marcelvanherk/nova1200-restoration/teensy_nova/Photo_Teensy40.jpg

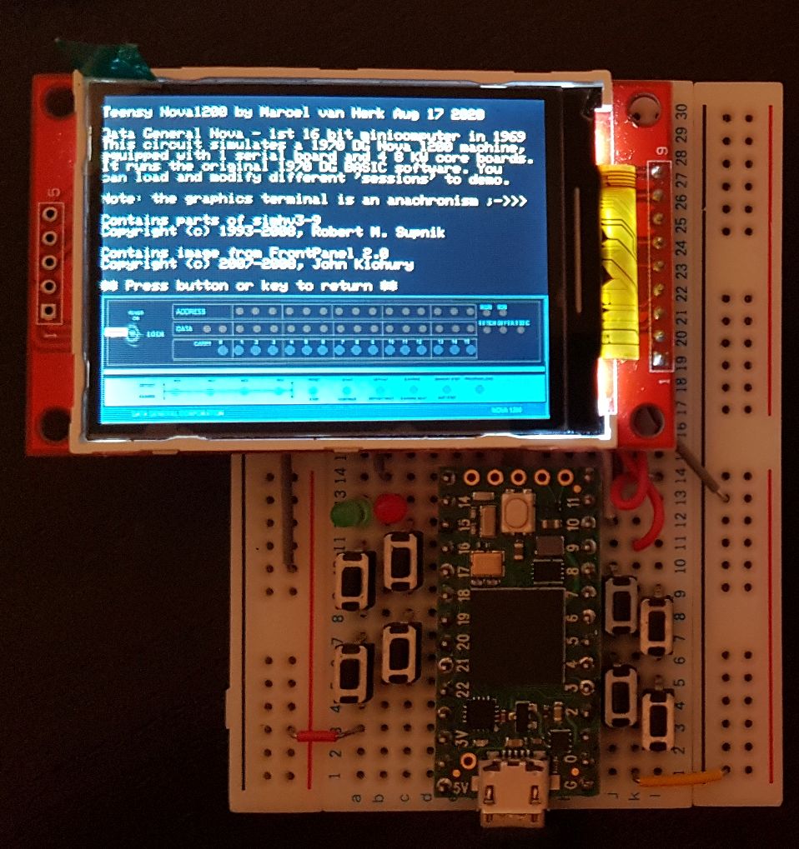
teensy_nova/Photo_Teensy40.jpg
