marcelvanherk/nova1200-restoration/teensy_nova/Pico_nova_bb.png

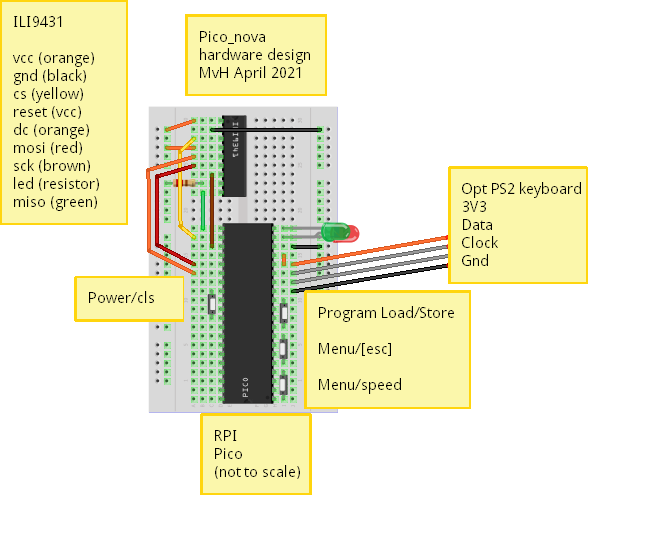
teensy_nova/Pico_nova_bb.png
