marcelvanherk/nova1200-restoration/teensy_nova/teensy_nova_bb.png

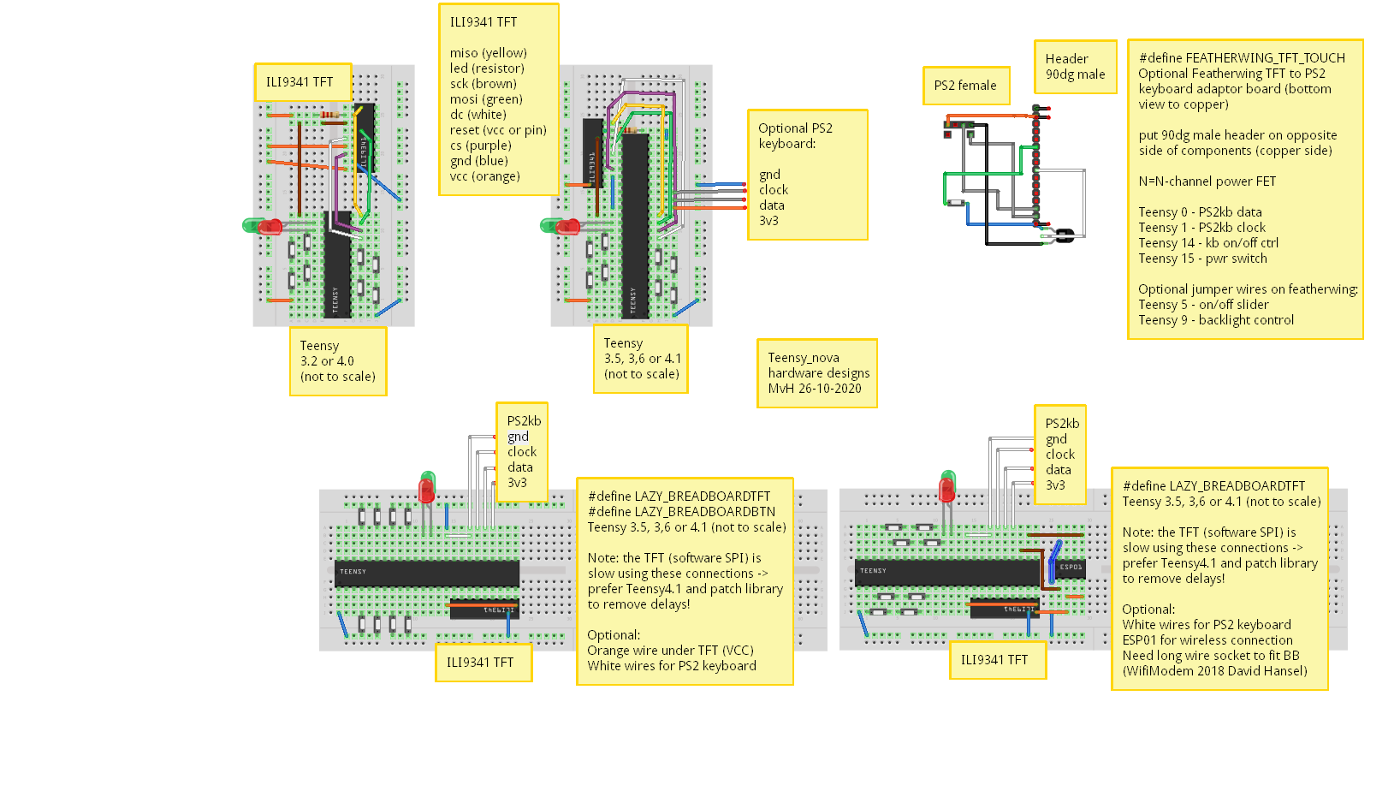
teensy_nova/teensy_nova_bb.png
