marcelvanherk/nova1200-restoration/arduino_nova1200rev3pcb/Minimal_components.png

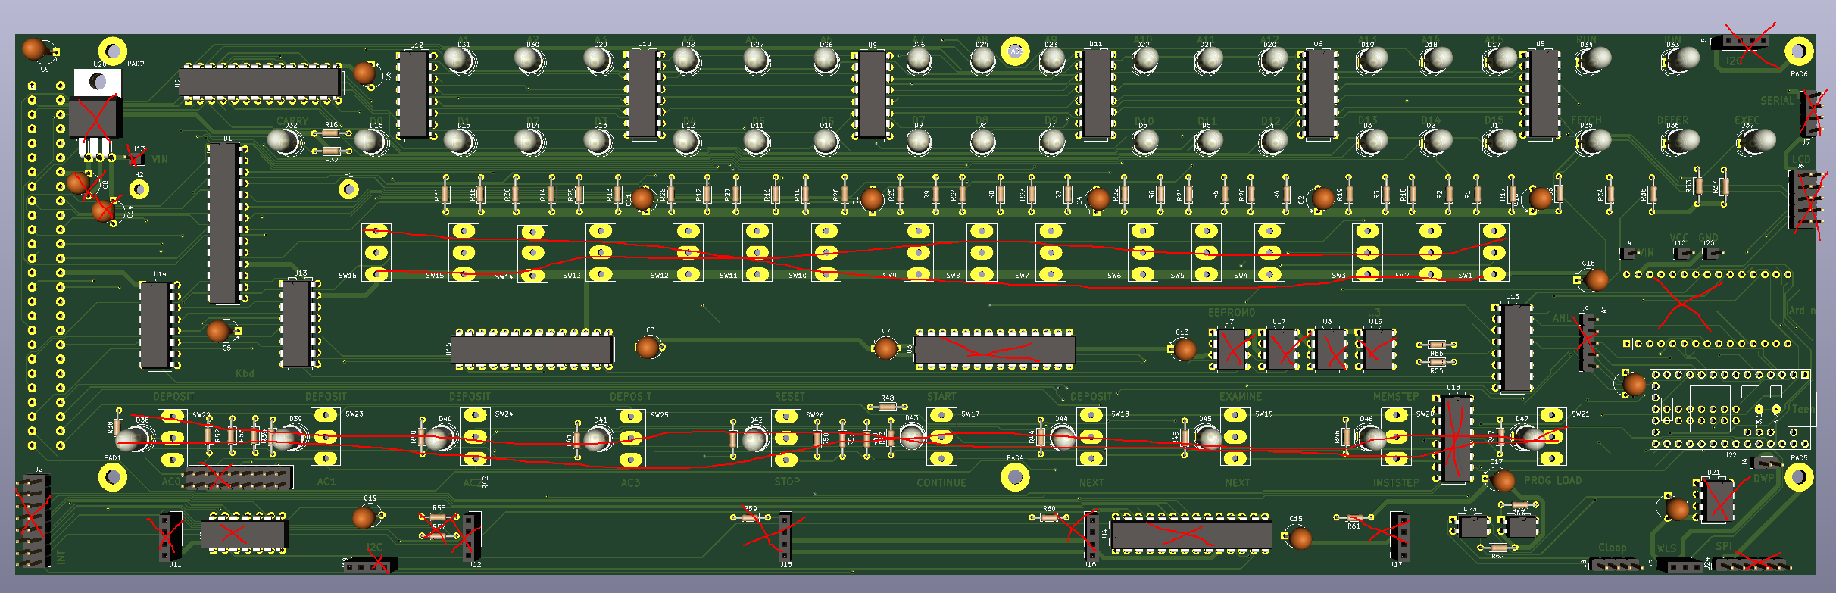
arduino_nova1200rev3pcb/Minimal_components.png
