marcelvanherk/nova1200-restoration/teensy_nova/recondemo.h

// demo version of nova reconstructor NovaReconstructDemo.lua
// Marcel van Herk 21 Jab 2025
// start with go 02000
// configurable variables start at address 02001
// 2501222 added sinogram display
// 2501225 sinogram displays right-hand; redisplay at 2015; load at 2017

const PROGMEM unsigned short recondemo[] = {

//>unload
53224,0,
32768,64,0,
64,13,1248,1528,1423,0,0,2048,7356,0,1806,15360,416,0,0,
77,2,596,90,
32847,4,0,
83,12,1388,128,1610,8970,272,1796,1578,9118,1593,4,1814,8576,
95,12,1028,1541,1567,1,2047,80,0,0,1993,1030,2,6400,
107,12,1033,100,0,1034,65280,1026,180,1050,255,0,59136,0,
119,12,1031,1518,0,1835,1032,70,0,0,1025,61440,61952,62464,
131,12,62976,63488,64000,64512,336,1000,0,98,0,170,65408,10,
143,9,66,0,248,64,0,65520,0,65436,1035,
32920,4,0,
156,2,1780,1615,
32926,17,0,
175,2,16,1854,
32945,210,0,
387,12,65394,65255,65118,64985,64853,64725,64599,64476,64355,64238,64123,64012,
399,1,63903,
33168,16,0,
416,12,32,65426,65287,65150,65017,64885,64757,64631,64508,64387,64270,64155,
428,12,64044,63935,63830,63727,63627,63531,63437,63347,63260,63176,63096,63018,
440,12,62944,62873,62806,62742,62681,62624,62570,62519,62472,62428,62388,62351,
452,12,62317,62288,62261,62238,62219,62203,62191,62182,62177,62175,62177,62182,
464,12,62191,62203,62219,62238,62261,62288,62317,62351,62388,62428,62472,62519,
476,12,62570,62624,62681,62742,62806,62873,62944,63018,63096,63176,63260,63347,
488,12,63437,63531,63627,63727,63830,63935,64044,64155,64270,64387,64508,64631,
500,12,64757,64885,65017,65150,65287,65426,32,176,323,472,623,777,
512,12,933,1091,1252,1414,1579,1746,1914,2085,2257,2431,2607,2785,
524,12,2964,3145,3328,3512,3697,3884,4072,4262,4452,4644,4837,5031,
536,12,5226,5421,5618,5815,6013,6212,6412,6612,6812,7013,7214,7416,
548,12,7618,7820,8022,8224,8426,8628,8830,9032,9234,9435,9636,9836,
560,12,10036,10236,10435,10633,10830,11027,11222,11417,11611,11804,11996,12186,
572,12,12376,12564,12751,12936,13120,13303,13484,13663,13841,14017,14191,14363,
584,12,14534,14702,14869,15034,15196,15357,15515,15671,15825,15976,16125,16272,
596,12,0,458,915,1372,1829,2285,2740,3195,3648,4101,4552,5002,
608,12,5450,5897,6342,6785,7226,7664,8101,8535,8966,9394,9820,10243,
620,12,10662,11079,11492,11901,12307,12709,13107,13501,13892,14277,14659,15036,
632,12,15408,15776,16139,16497,16850,17198,17541,17878,18210,18536,18857,19172,
644,12,19481,19784,20081,20372,20657,20936,21208,21474,21733,21985,22231,22470,
656,12,22702,22928,23146,23357,23561,23758,23948,24130,24306,24473,24633,24786,
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
//Length (words): 1828
};
