marcelvanherk/nova1200-restoration/teensy_nova/nova_sinogram3.h

// CT 180 projections 1.17 mm detector pitch

const PROGMEM unsigned short nova_sinogram3[]={

1,1,1,1,1,1,1,1,1,1,1,2,2,3,7,26,24,100,410,252,76,65,61,60,58,57,58,60,57,57,54,50,49,77,173,256,333,478,651,658,669,705,735,757,787,812,838,843,863,865,868,883,881,889,911,913,909,905,899,873,850,854,865,870,876,896,897,881,899,912,881,875,886,885,873,877,876,878,881,872,879,890,881,871,869,867,869,869,843,798,793,798,820,824,790,739,700,697,598,425,329,210,69,50,50,51,52,53,54,57,60,70,195,429,167,9,5,4,3,3,2,2,2,2,2,1,2,1,
1,1,1,1,1,1,1,1,1,1,1,2,2,3,15,28,18,167,418,206,68,62,62,61,58,57,59,60,57,57,53,50,52,91,185,265,347,506,654,653,664,706,734,752,777,804,834,840,845,867,868,882,887,884,903,914,911,907,905,889,863,857,867,874,876,882,901,896,887,904,891,872,874,887,875,873,874,870,880,876,874,882,889,883,880,873,867,863,847,809,790,801,817,831,796,738,712,698,568,404,318,199,69,49,50,51,52,52,55,57,62,80,246,381,117,6,4,4,3,3,2,2,2,2,2,2,1,1,
1,1,1,1,1,1,1,1,1,1,1,2,2,6,22,23,27,242,395,177,62,59,62,61,59,58,59,61,58,56,52,50,55,105,196,274,361,535,659,648,662,706,732,745,767,795,823,829,827,860,872,880,889,884,895,913,911,910,908,902,881,865,869,877,876,876,898,908,884,886,898,875,869,881,883,869,869,868,874,883,875,877,894,895,887,876,864,857,848,823,794,799,813,836,802,740,724,702,540,384,308,186,67,49,50,51,52,53,56,58,65,101,283,324,87,2,2,3,3,2,2,2,2,2,2,1,1,1,
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

};
