marcelvanherk/nova1200-restoration/teensy_nova/nova_sinogram4.h

// CT 180 projections 1.17 mm detector pitch

const PROGMEM unsigned short nova_sinogram4[]={

1,1,1,1,1,1,1,1,1,4,12,11,5,3,3,4,7,121,420,236,73,63,60,59,57,57,58,58,56,56,53,49,50,89,213,348,396,439,549,631,639,684,732,775,804,835,829,840,887,901,916,943,939,925,916,906,901,894,887,880,874,783,683,667,687,713,726,790,805,749,740,743,703,692,802,829,832,865,893,902,900,902,908,915,920,887,846,830,841,827,779,726,753,769,753,736,654,537,453,405,341,220,83,50,50,50,50,52,52,54,61,73,227,425,138,7,4,4,3,3,2,2,2,2,2,1,1,1,
1,1,1,1,1,1,1,1,4,12,12,5,2,3,3,4,12,191,417,194,65,61,60,59,58,57,58,59,56,56,52,49,55,106,214,340,400,455,573,630,648,692,734,779,801,821,828,847,889,905,920,945,943,931,919,909,905,897,893,884,875,804,693,659,665,705,734,776,806,761,743,743,731,697,770,826,830,861,889,897,899,905,911,915,911,882,839,819,839,829,786,747,765,759,752,724,628,516,445,400,339,214,88,50,50,50,50,51,52,56,63,87,275,369,96,5,3,3,3,2,2,2,2,2,2,2,1,1,
1,1,1,1,1,1,1,4,12,11,5,2,2,3,3,3,30,264,387,167,61,58,61,60,58,57,58,59,57,55,52,49,61,124,213,332,404,472,597,629,657,699,737,782,794,807,818,848,886,907,925,947,947,936,921,911,909,901,898,888,874,824,707,659,648,691,737,768,799,769,743,744,749,715,742,824,830,856,885,896,903,908,911,910,900,876,833,813,833,829,790,775,773,749,752,709,605,496,436,396,336,208,91,50,49,49,50,51,53,58,66,112,304,308,69,1,2,3,3,2,2,2,2,2,2,1,1,1,
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

};
