marcelvanherk/nova1200-restoration/teensy_nova/nova_sinogram2.h

// CT 180 projections 2.06 mm detector pitch

const PROGMEM unsigned short nova_sinogram2[]={

2,2,2,1,2,2,2,2,2,2,2,2,2,3,3,3,3,3,2,5,9,13,19,20,70,103,115,265,359,358,441,638,764,792,786,816,875,881,874,885,906,933,950,959,966,971,975,979,989,1002,1013,1021,1026,1030,1036,1039,1041,1048,1057,1065,1071,1076,1080,1086,1101,1107,1102,1092,1081,1074,1069,1062,1055,1049,1045,1044,1040,1037,1034,1028,1021,1012,1002,989,982,977,972,968,967,959,940,931,916,887,874,895,892,874,880,781,533,369,319,268,210,77,10,19,25,20,14,10,6,4,4,4,4,3,3,3,3,3,3,2,2,2,2,2,
1,2,2,2,1,2,2,2,2,2,2,3,3,3,3,3,3,3,3,2,5,8,11,18,48,108,113,203,346,415,450,608,760,807,803,839,888,876,869,885,906,926,946,958,964,970,975,981,993,1005,1014,1022,1025,1032,1036,1038,1043,1050,1057,1064,1069,1073,1078,1094,1105,1110,1103,1088,1081,1076,1068,1061,1057,1052,1047,1045,1040,1038,1034,1028,1022,1012,999,991,984,978,973,971,968,958,950,935,911,883,880,892,871,849,871,795,562,379,282,222,208,146,33,9,22,28,23,15,11,6,4,4,4,3,3,3,3,3,3,2,2,2,2,2,
0,1,2,2,2,2,2,2,2,3,3,3,3,3,3,3,3,3,3,2,2,4,7,8,23,93,124,188,292,402,485,610,756,822,820,866,902,868,864,885,905,921,937,953,963,969,975,985,997,1006,1015,1020,1027,1033,1035,1038,1046,1052,1056,1061,1066,1071,1084,1096,1105,1110,1100,1089,1081,1075,1068,1062,1057,1054,1050,1045,1042,1038,1033,1028,1022,1010,999,993,987,979,974,973,967,958,952,939,905,882,882,888,853,827,858,811,594,392,287,180,149,172,104,16,9,21,28,24,15,11,6,4,4,3,3,3,3,3,3,2,2,2,2,2,
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
};
