marcelvanherk/nova1200-restoration/teensy_nova/sos_xbasic.tape.h

// SOS Extended BASIC Interpreter from 1976; courtesy Bruce Ray

// values betweem {} created in lua as follows:
//local f = io.open([[E:\software\nova1200-restoration\SOS_XBASIC.AB]], 'rb')
//local t = f:read('*a')
//f:close()
//b={}
//for i=1, #t do
//  b[i]=t:byte(i)
//end
//print(#t, table.concat(b,','))

const PROGMEM unsigned char sos_xbasictape[]={0,0,0,0,0,0,0,0,0,0,0,0,0,0,0,0,0,0,0,0,0,0,0,0,0,0,0,0,0,0,0,0,0,0,0,0,0,0,0,0,0,0,0,0,0,0,0,0,0,0,0,0,0,0,0,0,0,0,
0,0,0,0,0,0,0,0,0,0,0,0,0,0,0,0,0,0,0,0,0,0,0,0,0,0,0,0,0,0,0,0,0,0,0,0,0,0,0,0,0,0,0,0,0,0,0,0,0,0,0,0,0,0,0,0,0,0,0,0,0,0,0,0,0,0,0,0,0,0,240,255,0,0,221,143,0,
0,222,7,12,9,37,8,47,8,0,0,240,4,0,0,207,8,180,8,0,1,54,2,182,254,52,50,0,0,98,4,0,0,0,0,240,255,16,0,44,255,0,0,0,0,2,0,3,0,4,0,5,0,6,0,7,0,0,0,10,0,13,0,16,0,32,
0,34,0,36,0,44,0,0,0,0,0,240,255,32,0,149,148,46,0,48,0,64,0,127,0,128,0,226,0,231,0,233,0,68,10,69,10,79,10,78,10,123,10,157,10,109,20,97,20,0,0,0,0,240,255,48,0,
71,179,99,20,101,20,103,20,107,20,145,20,105,20,66,20,0,21,249,20,9,21,12,21,64,21,241,20,234,20,84,21,70,21,0,0,0,0,240,255,64,0,46,10,110,21,112,21,118,21,0,0,0
,0,0,0,0,0,155,21,41,22,43,22,44,22,47,23,85,23,94,23,81,23,0,0,0,0,0,0,240,255,80,0,9,129,191,23,175,23,0,0,3,24,95,24,141,26,129,27,132,27,135,27,102,28,207,29,
215,29,232,29,238,29,236,29,0,0,0,0,0,0,240,255,96,0,227,177,0,0,0,0,0,0,0,0,0,0,177,32,181,32,169,32,173,32,116,31,0,0,229,31,125,34,106,35,183,34,26,35,0,0,0,0,
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
,7,206,5,139,7,0,0,0,0,0,0,0,0,0,0,0,0,0,0,0,0,0,0,0,0,0,0,0,0,0,0,0,0,240,255,160,3,112,252,0,0,0,0,0,0,0,0,0,0,0,0,0,0,0,0,0,0,0,0,0,0,0,0,0,0,0,0,0,0,0,0,0,0,0,0,240
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
