marcelvanherk/nova1200-restoration/teensy_nova/novabasic2.tape.h

// single user basic 2 from 1971

const PROGMEM unsigned char basic2tape[]={0,0,0,0,0,0,0,0,0,0,0,0,0,0,0,0,
248,255,0,0,25,40,2,0,99,1,3,4,58,15,231,64,
218,64,230,64,166,0,240,255,16,0,28,254,0,0,3,0,
4,0,5,0,6,0,7,0,10,0,11,0,15,0,18,0,
20,0,64,0,65,0,81,0,85,0,90,0,240,255,32,0,
248,245,94,0,124,0,127,0,128,0,135,0,138,0,141,0,
152,0,155,0,160,0,164,0,176,0,197,0,218,0,220,0,
223,0,240,255,48,0,228,117,224,0,226,0,228,0,231,0,
233,0,234,0,235,0,237,0,239,0,242,0,244,0,246,0,
252,0,254,0,255,0,0,124,253,255,64,0,183,114,0,255,
138,141,130,0,240,255,72,0,131,112,217,2,56,9,24,13,
25,13,119,12,135,12,152,12,97,11,182,3,189,4,43,1,
62,1,57,12,13,12,114,11,120,9,240,255,88,0,53,144,
176,11,177,10,158,11,132,11,105,1,22,7,29,9,149,11,
143,5,99,2,88,11,222,1,146,7,61,2,174,3,42,2,
246,255,104,0,130,218,223,7,161,2,134,0,32,2,150,1,
65,11,150,2,111,3,157,3,129,1,240,255,138,0,2,34,
0,0,0,0,0,0,0,0,224,48,224,16,147,0,228,48,
228,16,144,210,0,42,3,170,192,170,62,48,0,183,216,32,
241,255,154,0,191,161,41,40,5,130,12,181,0,3,255,3,
45,32,245,40,26,197,26,205,0,3,0,181,1,3,127,96,
167,0,0,0,240,255,170,0,109,178,251,0,249,0,241,0,
248,0,232,0,250,0,52,11,56,11,44,11,48,11,185,10,
120,2,202,10,119,2,0,0,0,0,240,255,186,0,84,129,
0,0,0,0,0,0,0,0,0,0,0,0,58,15,87,15,
88,15,126,15,152,15,158,15,160,15,171,15,253,0,29,1,
243,255,202,0,251,171,60,1,58,15,58,15,86,15,87,15,
112,1,109,2,41,2,44,2,183,12,2,0,0,0,0,0,
240,255,232,0,143,187,174,0,162,0,188,190,190,0,190,189,
189,0,188,189,188,0,187,0,172,0,168,0,219,0,172,0,
192,0,169,0,221,0,249,255,248,0,128,251,173,0,171,0,
175,0,170,0,222,0,0,0,0,0,240,255,63,1,122,237,
6,33,43,40,26,197,26,204,0,3,1,3,185,0,67,79,
80,89,82,73,71,72,84,32,40,67,41,32,49,57,54,57,
240,255,79,1,43,91,44,49,57,55,48,44,49,57,55,49,
44,49,57,55,50,44,49,57,55,51,65,76,76,32,82,73,
71,72,84,83,32,82,240,255,95,1,186,225,69,83,69,82,
86,69,68,0,67,64,68,72,69,80,70,88,112,133,71,64,
255,103,16,1,200,103,82,1,201,103,24,1,240,255,111,1,
128,210,63,99,4,130,63,102,71,32,128,130,67,32,68,40,
69,48,70,56,127,96,0,4,0,32,5,65,3,33,0,64,
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
