marcelvanherk/nova1200-restoration/teensy_nova/basic.session.h

const PROGMEM unsigned short basicsession[] = {
4938,0,
0,8,451,326,26047,34048,16615,16602,16614,166,
32776,9,0,
17,12,3,4,5,6,7,10,11,15,18,20,64,65,
29,12,81,85,90,94,124,127,128,135,138,141,152,155,
41,12,160,164,176,197,218,220,223,224,226,228,231,233,
53,12,234,235,237,239,242,244,246,252,254,255,31744,65280,
65,12,36234,130,0,65533,141,451,0,700,2331,3323,3324,3162,
77,12,3178,3195,2884,921,1184,299,318,3100,3056,2901,2395,2963,
89,12,2708,2945,2919,332,1785,2304,2936,1394,582,2875,449,1909,
101,12,544,913,525,1986,644,134,515,377,2852,633,850,896,
113,1,356,
32882,6,0,
120,2,3909,1,
32890,20,0,
142,12,12512,4320,147,12516,4324,53904,10752,43523,43712,12350,46848,8408,
154,12,10281,33285,46348,768,1023,8237,10485,50458,52506,768,46336,769,
166,12,24703,167,0,0,251,249,241,248,232,250,2839,2843,
178,6,2831,2835,2716,603,2733,602,
32952,8,0,
192,13,3869,32495,32496,32534,32560,32584,32592,32639,253,285,316,3869,3869,
205,12,32493,32495,368,592,524,527,3255,2,14,70,0,130,
217,2,0,1,
32987,4,0,
223,12,32495,634,32495,32592,32584,64992,133,0,0,174,162,48828,
235,12,190,48574,189,48572,188,187,172,168,219,172,192,169,
247,12,221,173,171,175,170,222,3338,3338,20310,17746,22354,18772,
259,12,17696,21576,17696,18005,20035,21577,20302,21280,21321,20012,17231,21292,
271,12,16724,20000,16718,17440,21569,20000,10324,22864,17696,22816,20306,8270,
283,12,10559,8192,3338,17487,8281,20309,8279,18771,18464,17231,19789,16679,
295,12,21280,21583,8258,17696,12596,8275,20545,17221,21280,10324,22864,17696,
307,12,22825,11296,20306,8241,13600,10324,22864,17696,20009,16128,0,0,
319,12,8454,10283,50458,52250,768,769,185,16451,18500,20549,22598,34160,
331,12,16455,26623,272,26568,338,26569,280,25407,33284,26175,8263,33408,
343,12,8259,10308,12357,14406,24703,1024,8192,16645,8451,16384,26175,1137,
355,12,0,8703,16384,34048,16615,493,24713,8423,33285,1116,12517,4325,
367,12,2195,20711,53765,259,2323,1116,10458,52229,24648,1116,26441,511,
379,12,16613,22759,16600,37376,2195,4325,24767,2308,14567,24703,768,22805,
391,12,8412,10454,35866,265,20753,12326,2320,12325,2318,12556,34048,16604,
403,12,10281,52251,4316,10277,52485,18652,2308,1281,372,0,26441,511,
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
