marcelvanherk/nova1200-restoration/teensy_nova/nova.image.h

/* GIMP RGB C-Source image dump (nova1200_fp.c) */

static const struct {
  unsigned int 	 width;
  unsigned int 	 height;
  unsigned int 	 bytes_per_pixel; /* 2:RGB16, 3:RGB, 4:RGBA */ 
  unsigned char	 pixel_data[320 * 93 * 2 + 1];
} gimp_image = {
  320, 93, 2,
  "\064\245\222\224\222\234\221\234\221\234\221\234\222\224\222\224\222\224\222"
  "\224\222\224\222\224\222\224\222\224\222\224\222\224\222\224\222\224\222"
  "\224\222\224\222\224\222\224\222\224\222\224\222\224\222\224\222\224\222"
  "\224\222\224\222\224\222\224\222\224\222\224\222\224\222\224\222\224\222"
  "\224\222\224\222\224\222\224\222\224\222\224\222\224\222\224\222\224\222"
  "\224\222\224\222\224\222\224\222\224\222\234\222\234\222\234\222\234\222"
  "\234\222\234\222\234\222\234\222\234\222\234\221\234\221\234\221\234\221"
  "\234\221\234\222\234\222\234\222\234\222\234\222\234\222\234\222\234\222"
  "\234\222\234\222\234\222\234\222\234\222\234\222\234\222\234\222\234\222"
  "\234\222\234\222\234\222\234\222\234\222\234\222\234\222\234\222\234\222"
  "\234\222\234\222\234\222\234\222\234\222\234\222\234\222\234\222\234\222"
  "\234\222\234\222\234\222\234\222\234\222\234\222\234\222\234\222\234\222"
  "\234\222\234\222\234\222\234\222\234\222\234\222\234\222\234\222\234\222"
  "\234\222\234\222\234\222\234\222\234\222\234\222\234\222\234\222\234\222"
  "\234\222\234\222\234\222\234\222\224\222\224\222\224\222\224\222\224\222"
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
  "\000\000\000\000\000\000\000\000\000\000\000\000\000\000\000\000\000\000\000\000\000\000\000\000\000\000\000\000\000\000\000\000\000\000\000\000"
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
